Scisaga/n305-case/pics/original-case.png

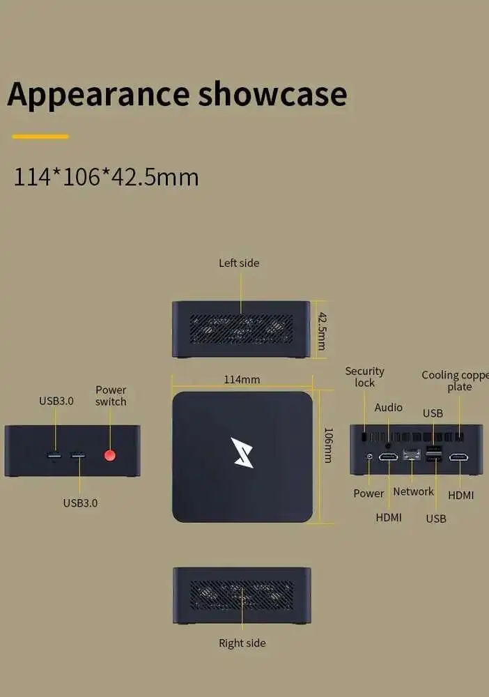
pics/original-case.png
