Scisaga/n305-case/pics/机箱盒子06.jpg

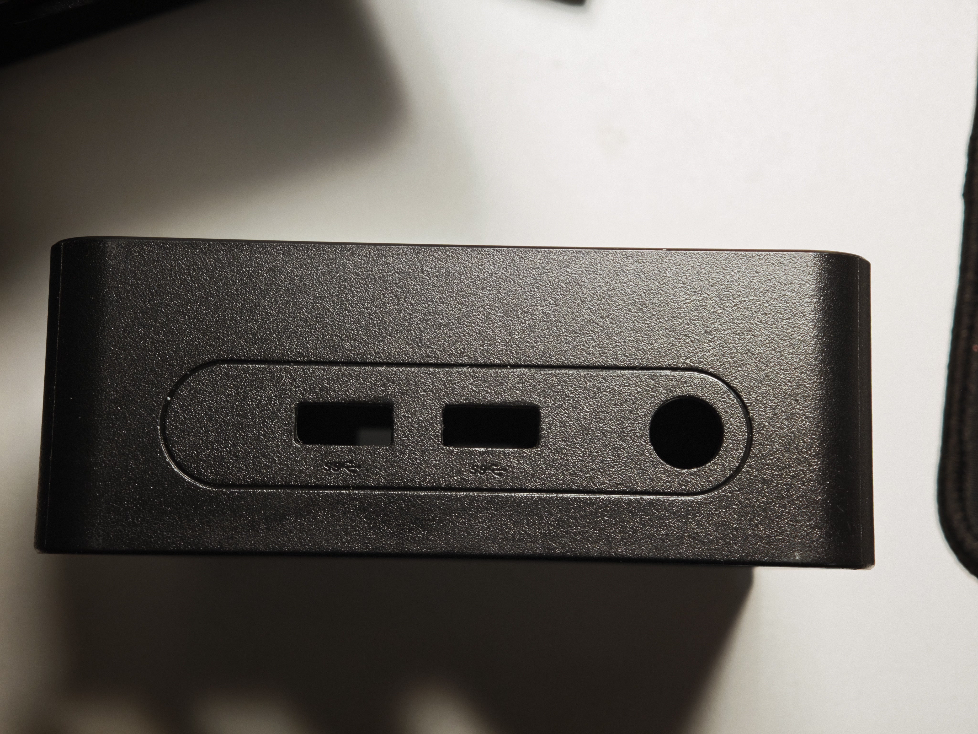
pics/机箱盒子06.jpg
