Scisaga/n305-case/previews/enclosure/aperture-coverage-review.png

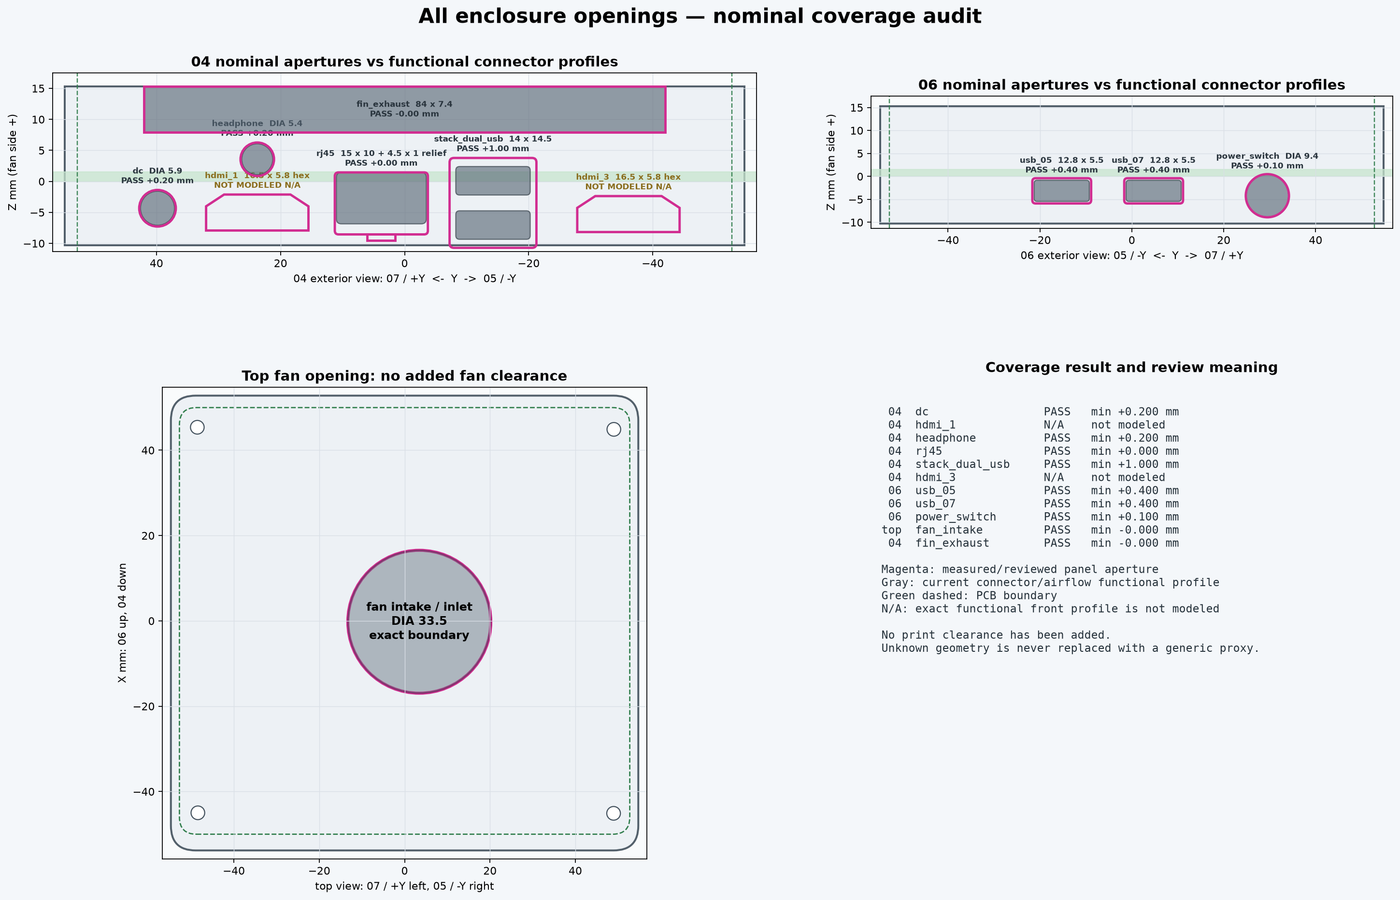
previews/enclosure/aperture-coverage-review.png
