Scisaga/n305-case/previews/enclosure/face-ownership-and-seam.png

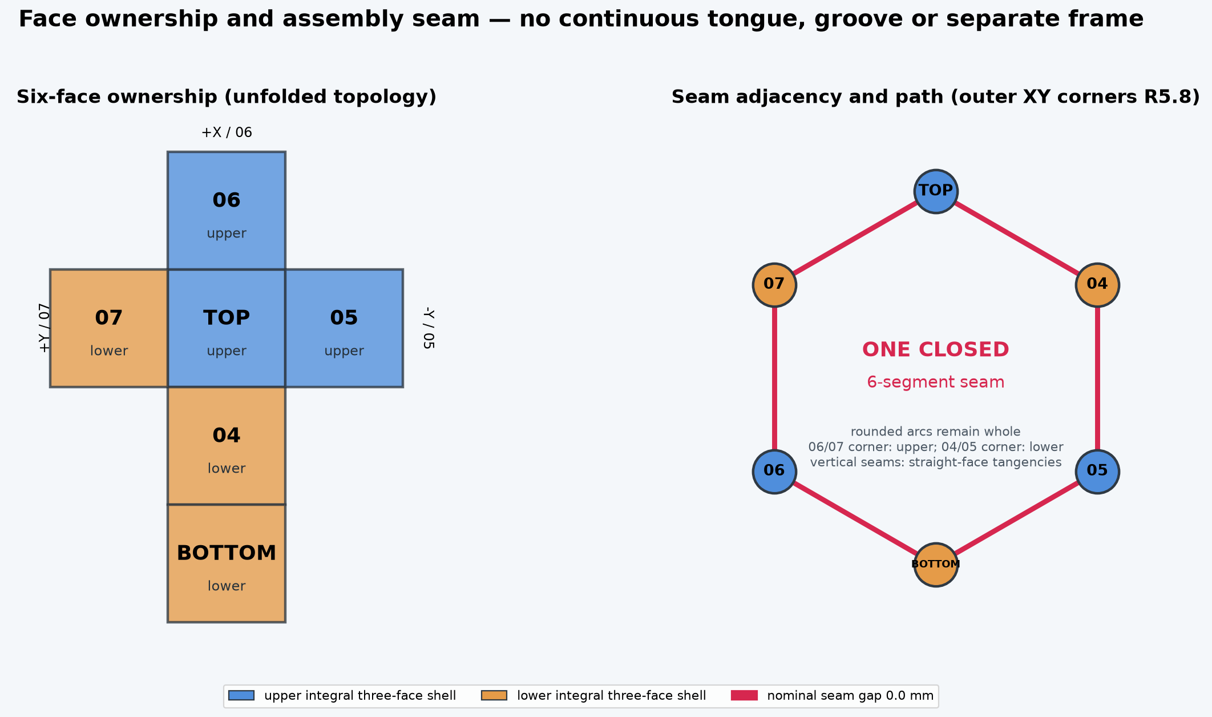
previews/enclosure/face-ownership-and-seam.png
