Scisaga/n305-case/previews/enclosure/reinforcement-inner-plan.png

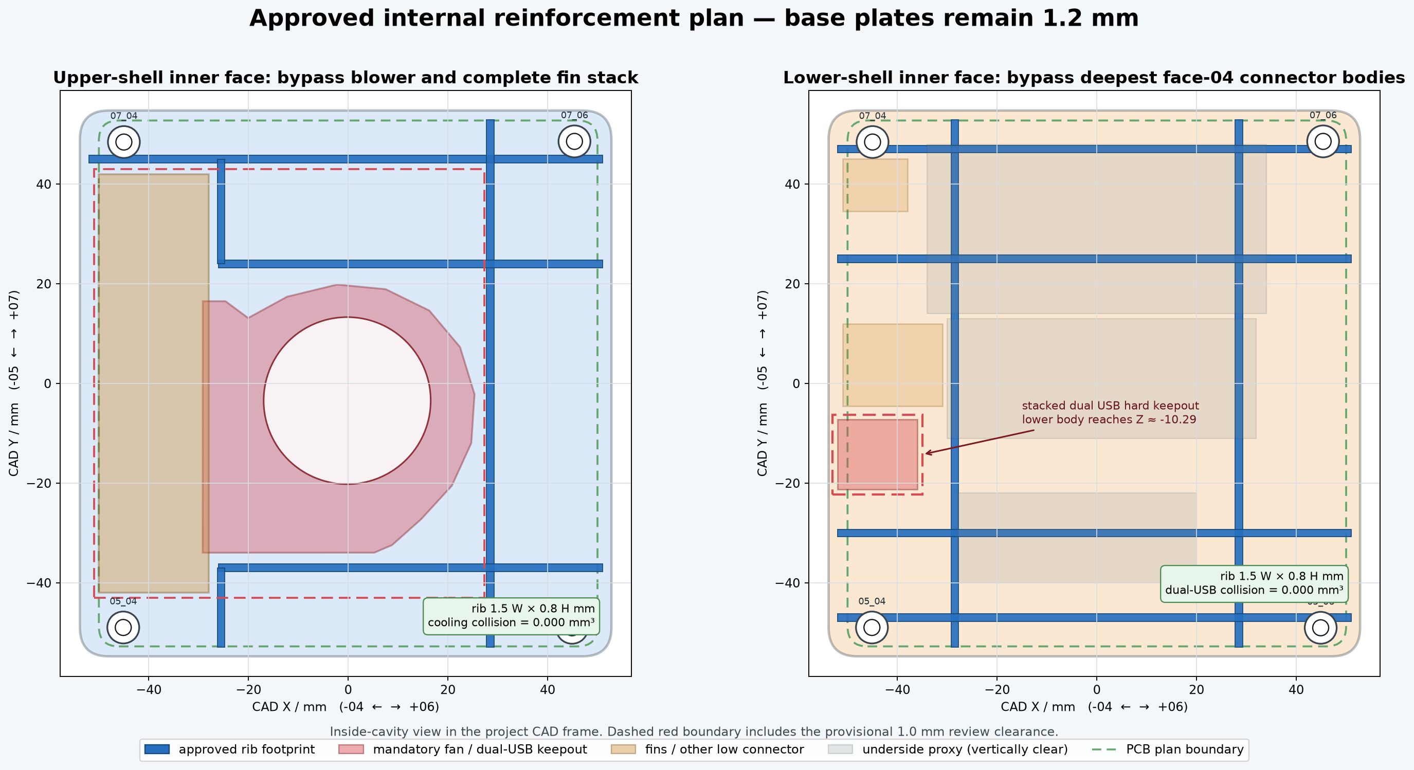
previews/enclosure/reinforcement-inner-plan.png
