Scisaga/n305-case/previews/enclosure/rounded-corner-seam-detail.png

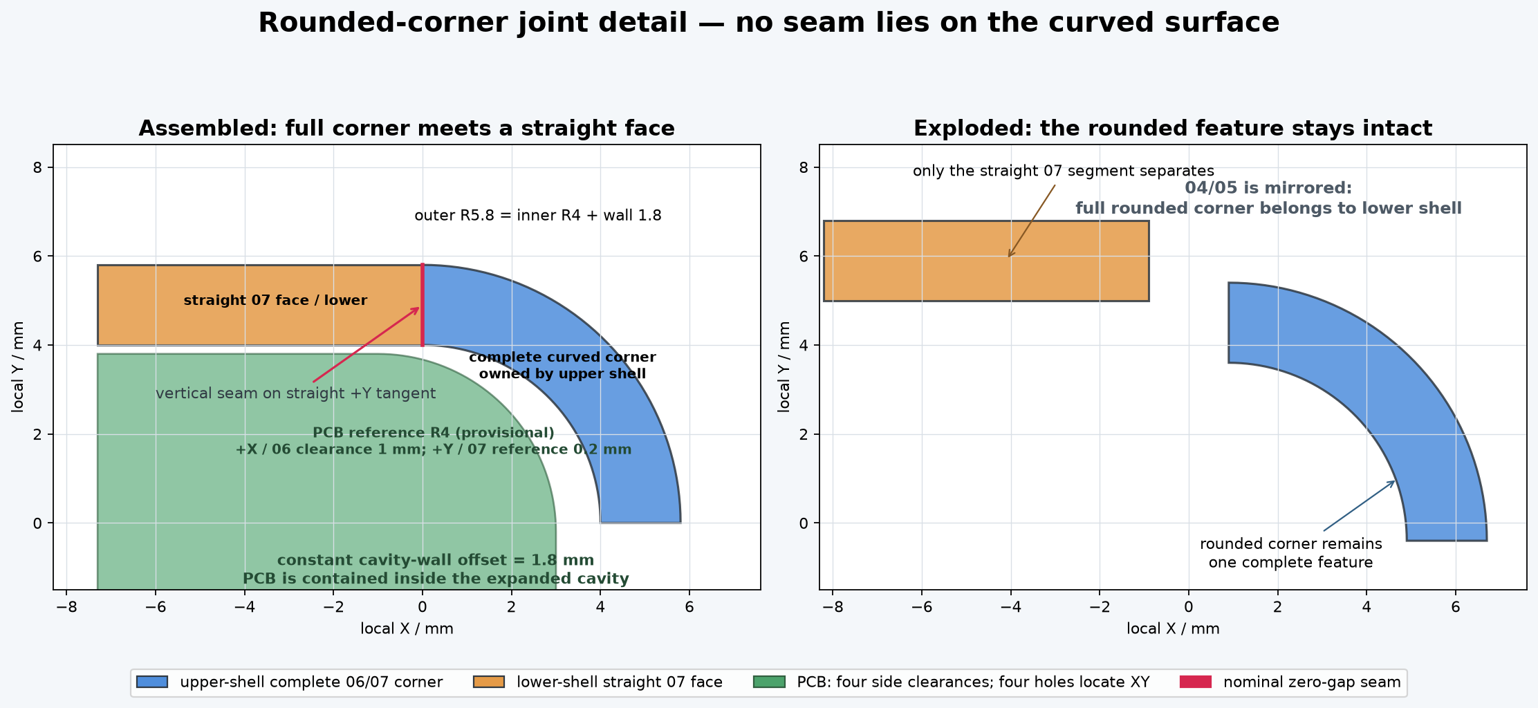
previews/enclosure/rounded-corner-seam-detail.png
