Scisaga/n305-case/previews/reference/06-interface-reference.png

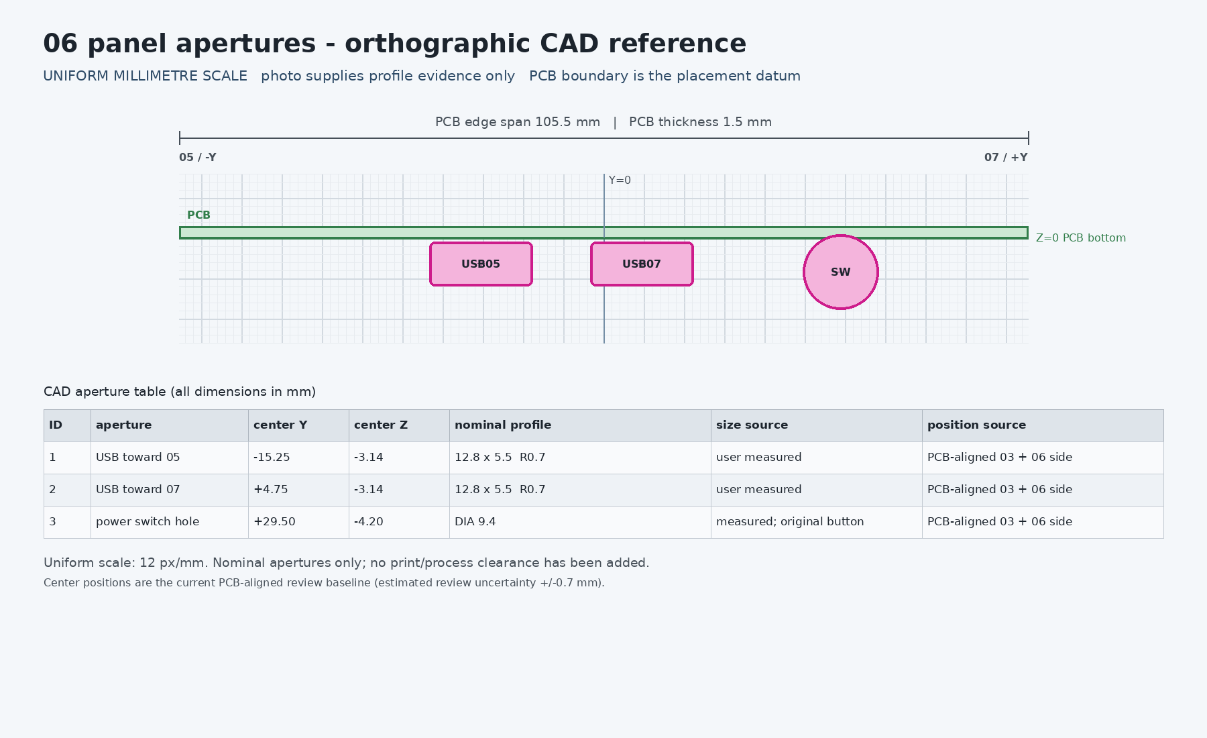
previews/reference/06-interface-reference.png
