Scisaga/n305-case/previews/reference/cooling-contact-path.png

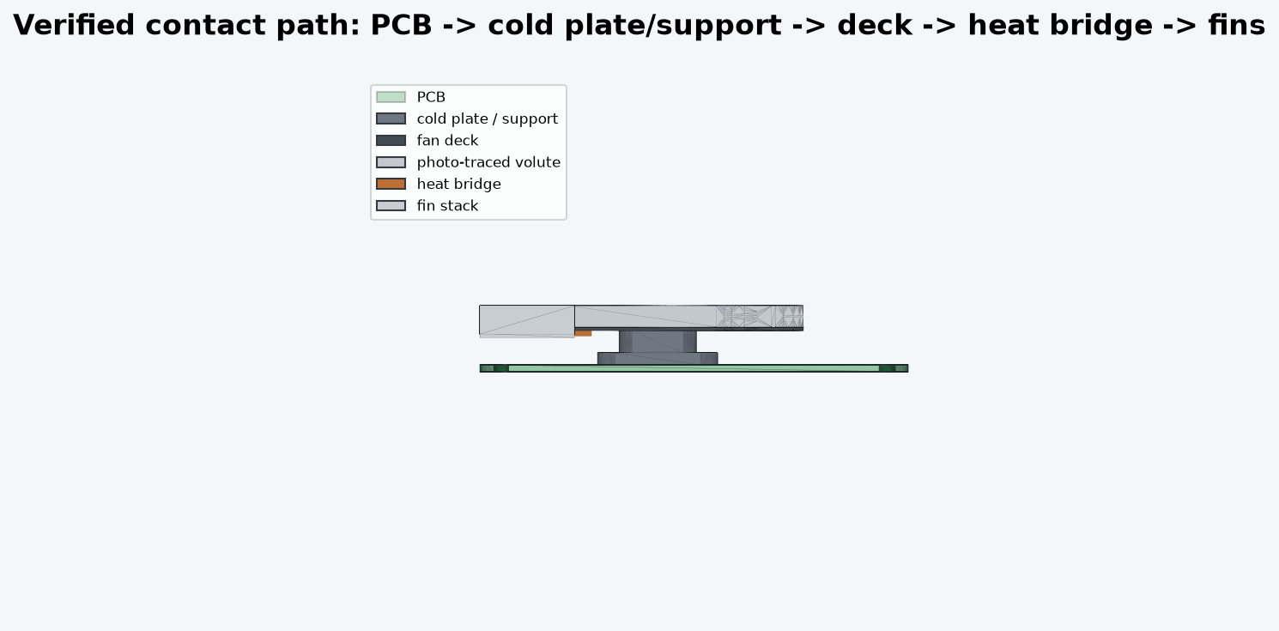
previews/reference/cooling-contact-path.png
