Scisaga/n305-case/previews/reference/motherboard-bottom.png

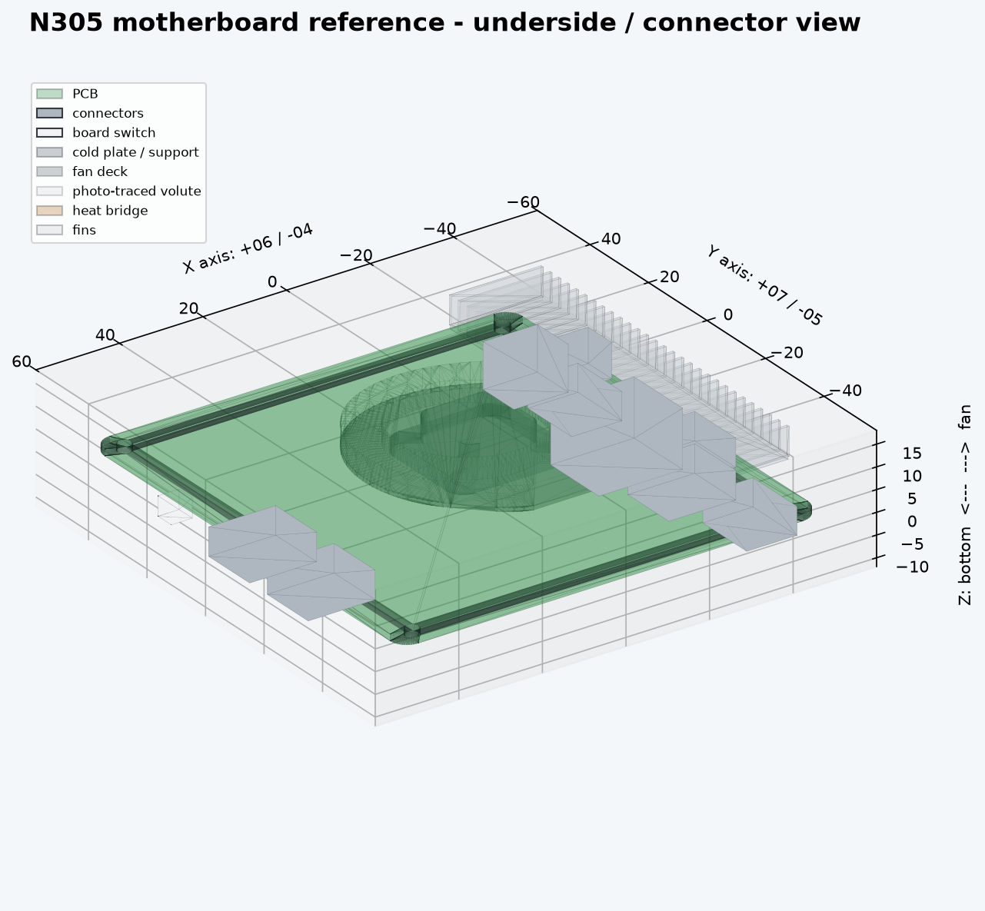
previews/reference/motherboard-bottom.png
