Scisaga/n305-case/previews/reference/motherboard-isometric.png

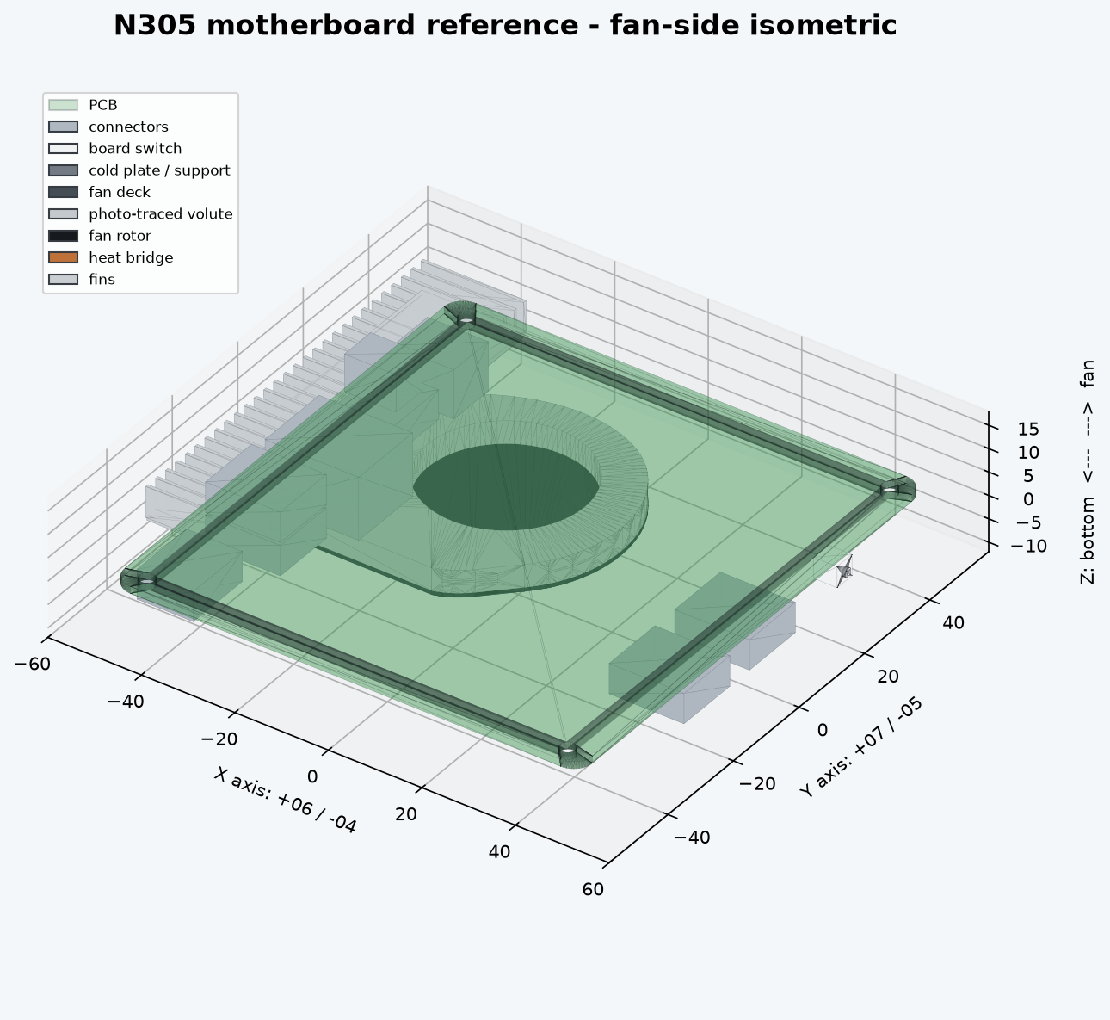
previews/reference/motherboard-isometric.png
