Scisaga/n305-case/previews/reference/motherboard-plan.png

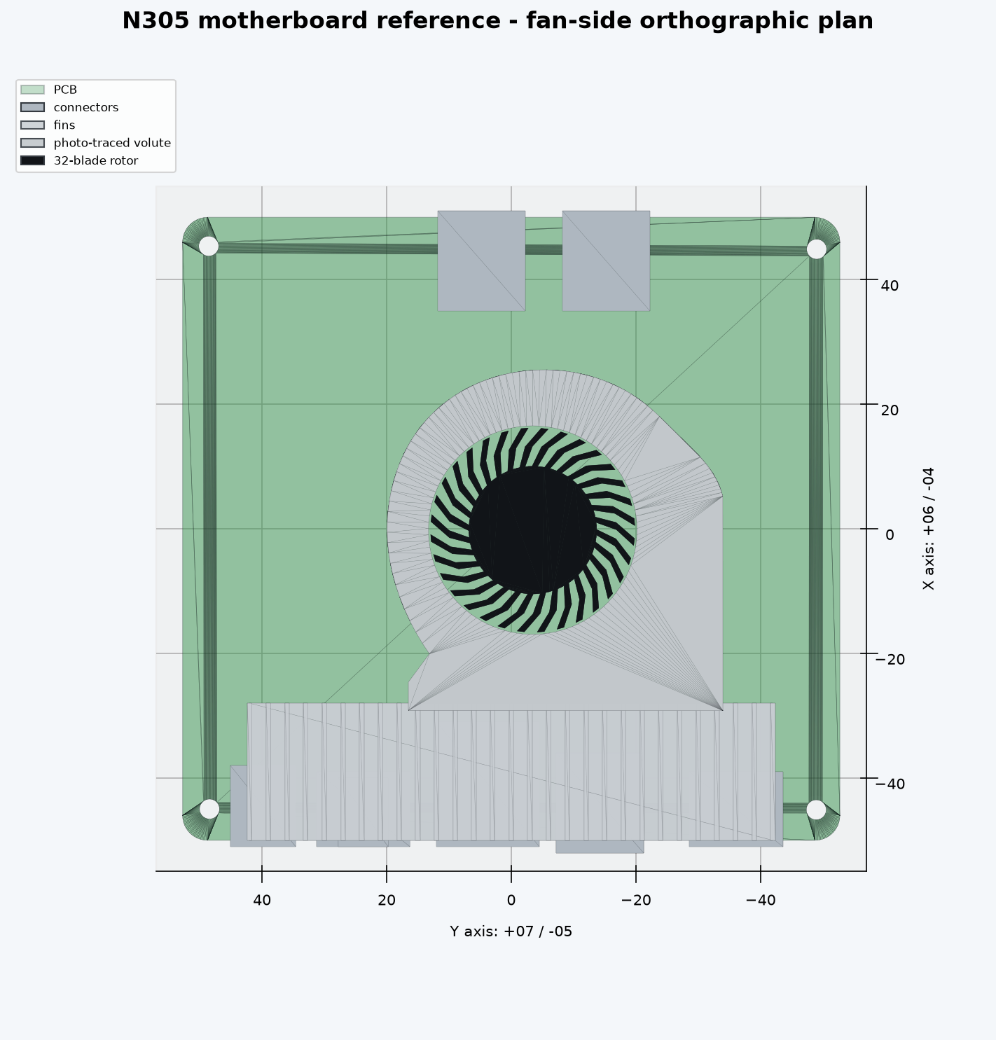
previews/reference/motherboard-plan.png
