Scisaga/n305-case/previews/calibration/original-case-04-1mm-grid.png

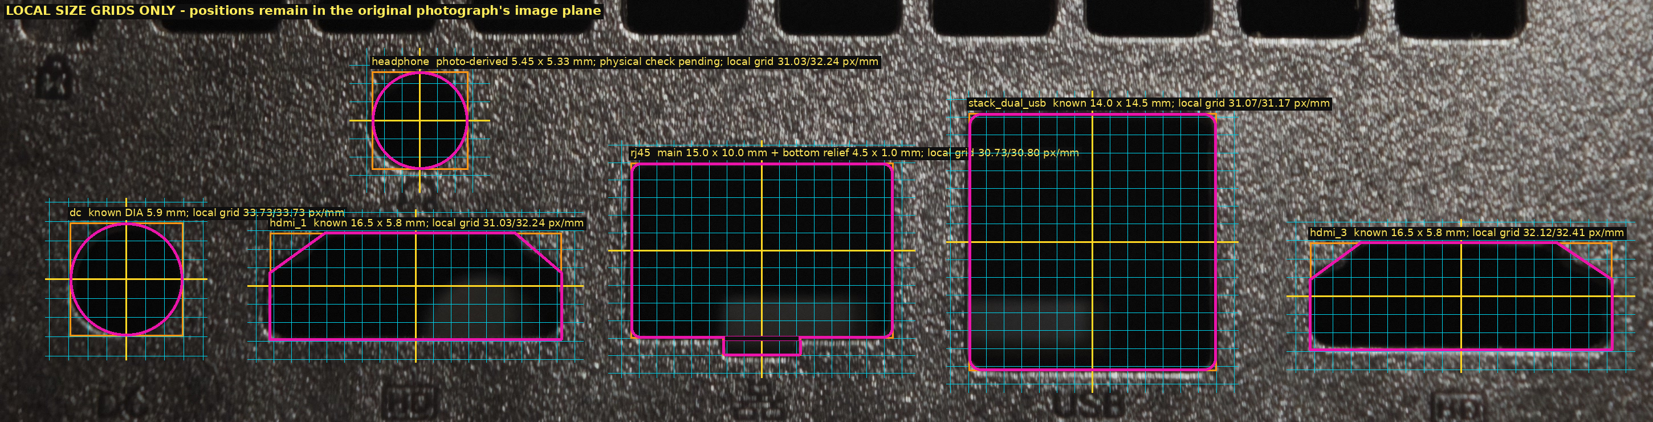
previews/calibration/original-case-04-1mm-grid.png
