Scisaga/n305-case/previews/calibration/original-case-04-dc-raw.png

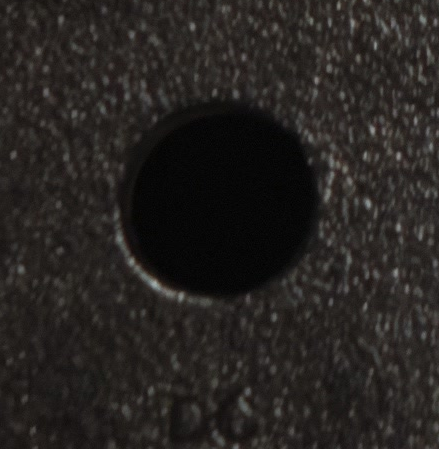
previews/calibration/original-case-04-dc-raw.png
