Scisaga/n305-case/previews/calibration/original-case-04-hdmi_3-raw.png

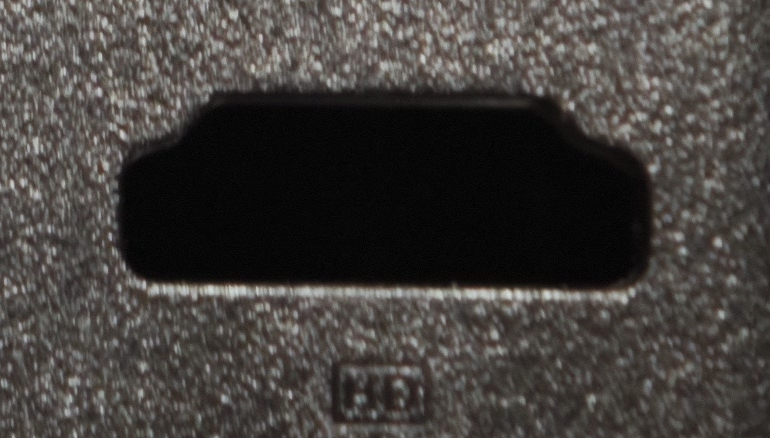
previews/calibration/original-case-04-hdmi_3-raw.png
