Scisaga/n305-case/previews/calibration/original-case-04-headphone-raw.png

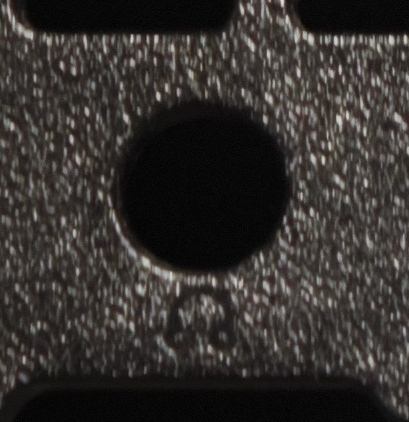
previews/calibration/original-case-04-headphone-raw.png
