Scisaga/n305-case/previews/calibration/original-case-04-rj45-raw.png

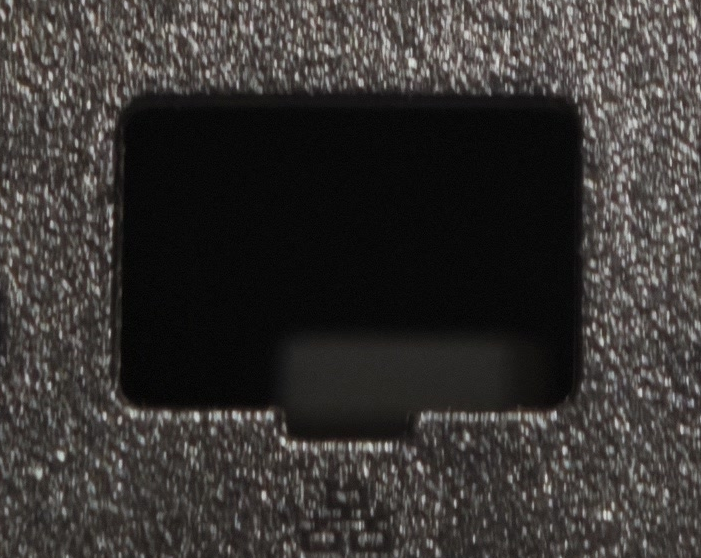
previews/calibration/original-case-04-rj45-raw.png
