Scisaga/n305-case/previews/calibration/original-case-06-usb_left-raw.png

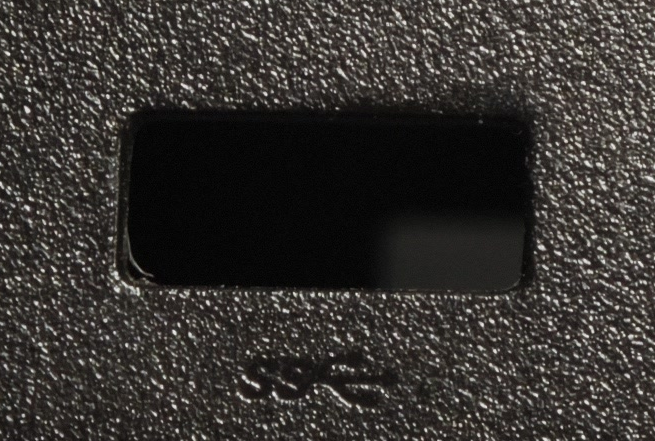
previews/calibration/original-case-06-usb_left-raw.png
